AnnaZavgorodnia/Gesture_controle_robot/code/1.0.5 stable final/robot/distance.h

#pragma once

int distance_by_direction(byte some_direction, int wait_time);
int distance_at_angle(byte angle, int wait_time);
int distance_backward();
byte scan(byte direction_scan, int wait_timeee);
